olanisgmbh/regreen_sensolab/Infografiken/sensolab_proto_1.jpg

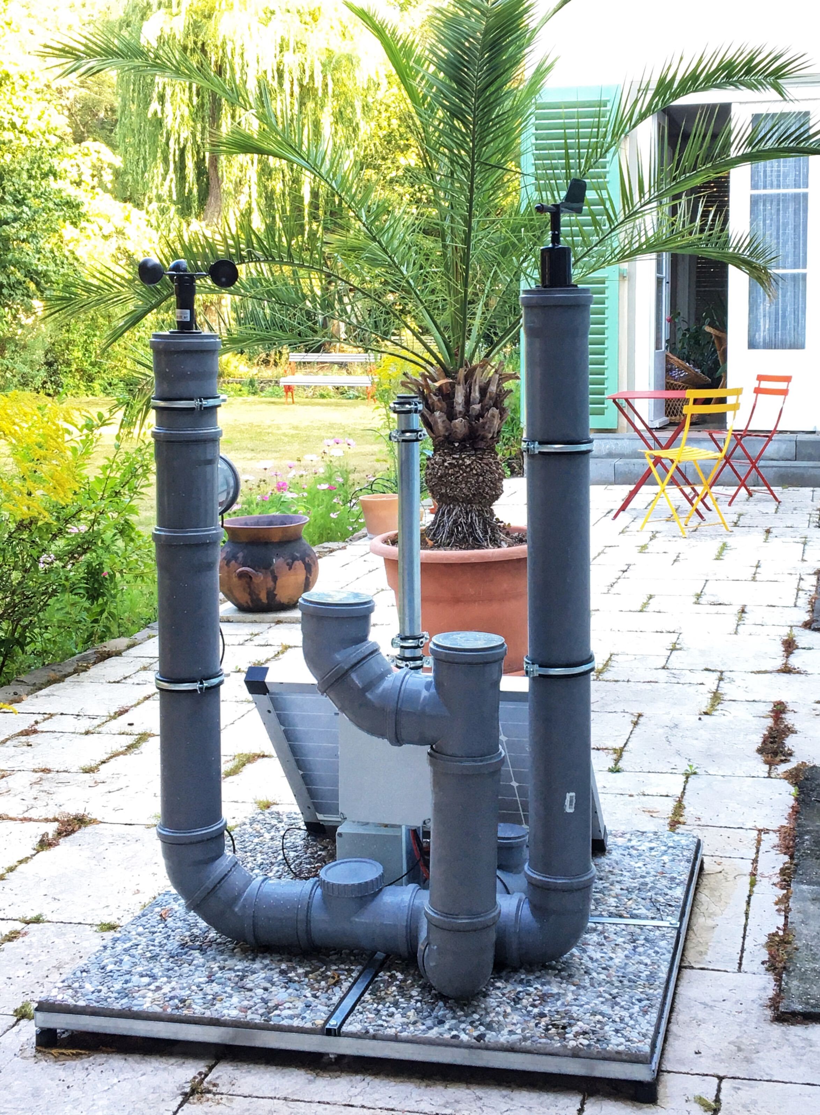
Infografiken/sensolab_proto_1.jpg
