olanisgmbh/regreen_sensolab/light-dome module/images/lightdome_01.jpg

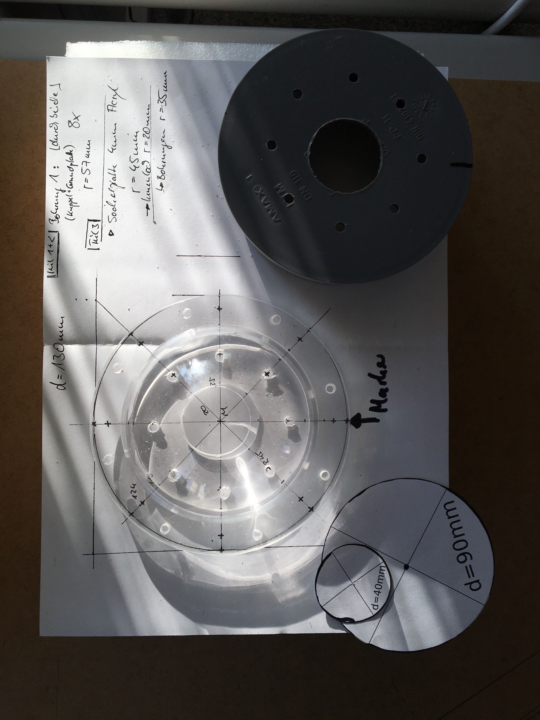
light-dome module/images/lightdome_01.jpg
