olanisgmbh/regreen_sensolab/light-dome module/KiCAD/Lightdome_SensorPCB/Lightdome_SensorPCB_wh.png

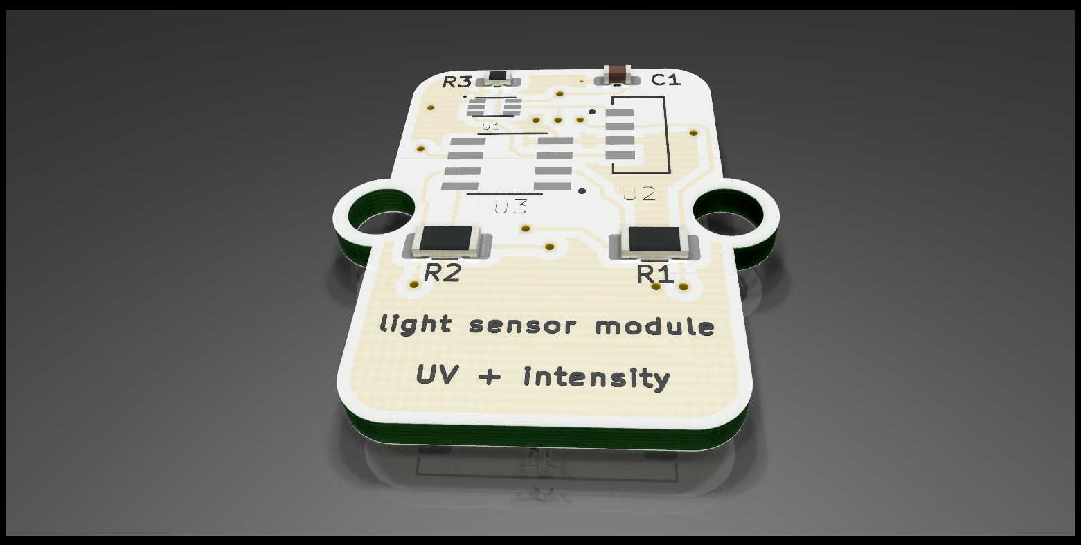
light-dome module/KiCAD/Lightdome_SensorPCB/Lightdome_SensorPCB_wh.png
