olanisgmbh/regreen_sensolab/LoRaWAN stuff/Screenshot at 2020-06-05 12-15-55.png

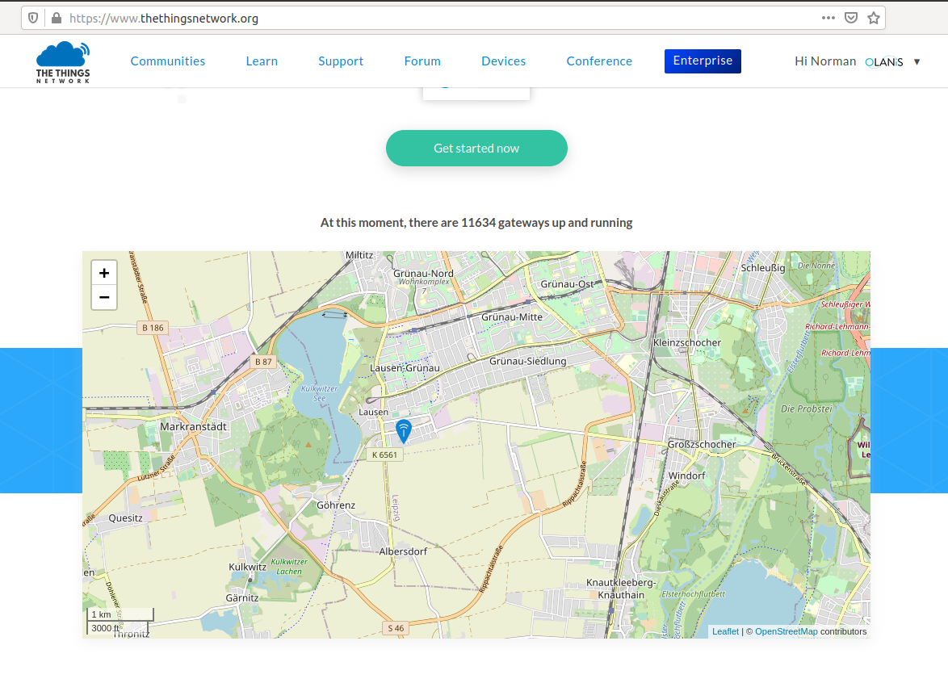
LoRaWAN stuff/Screenshot at 2020-06-05 12-15-55.png
