olanisgmbh/regreen_sensolab/LoRaWAN stuff/Screenshot at 2020-06-05 12-48-13.png

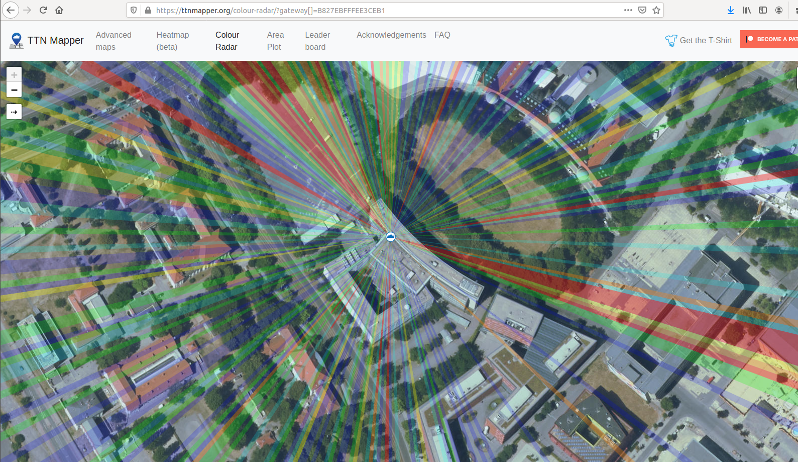
LoRaWAN stuff/Screenshot at 2020-06-05 12-48-13.png
