olanisgmbh/regreen_sensolab/LoRaWAN stuff/Screenshot at 2020-06-05 12-54-40.png

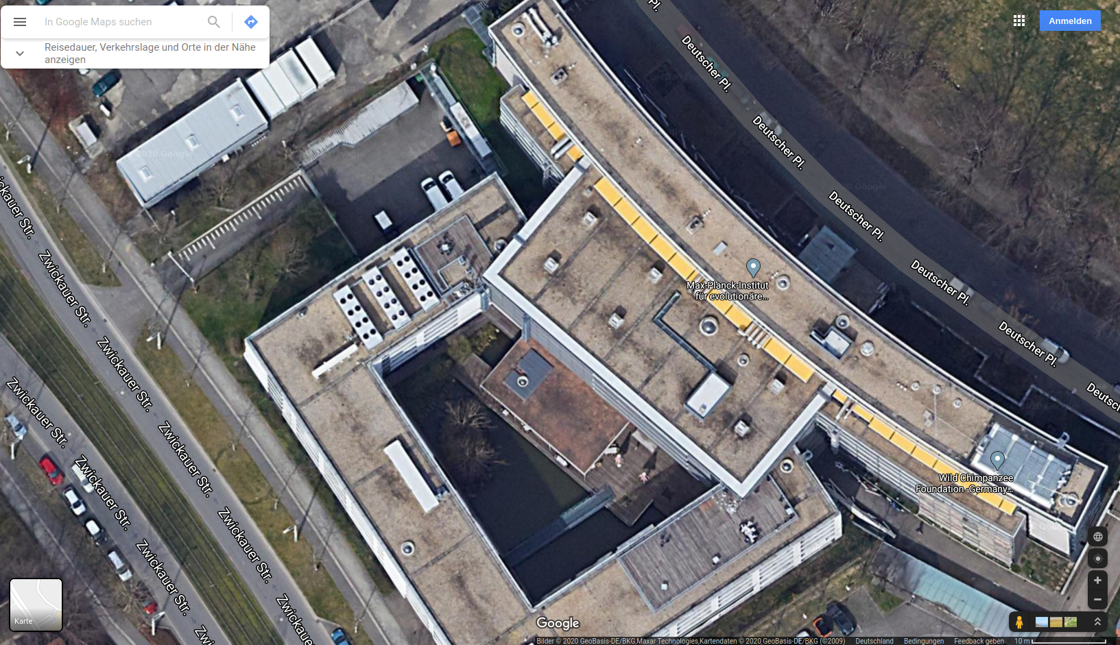
LoRaWAN stuff/Screenshot at 2020-06-05 12-54-40.png
