olanisgmbh/regreen_sensolab/LoRaWAN stuff/Screenshot at 2020-06-05 13-23-22.png

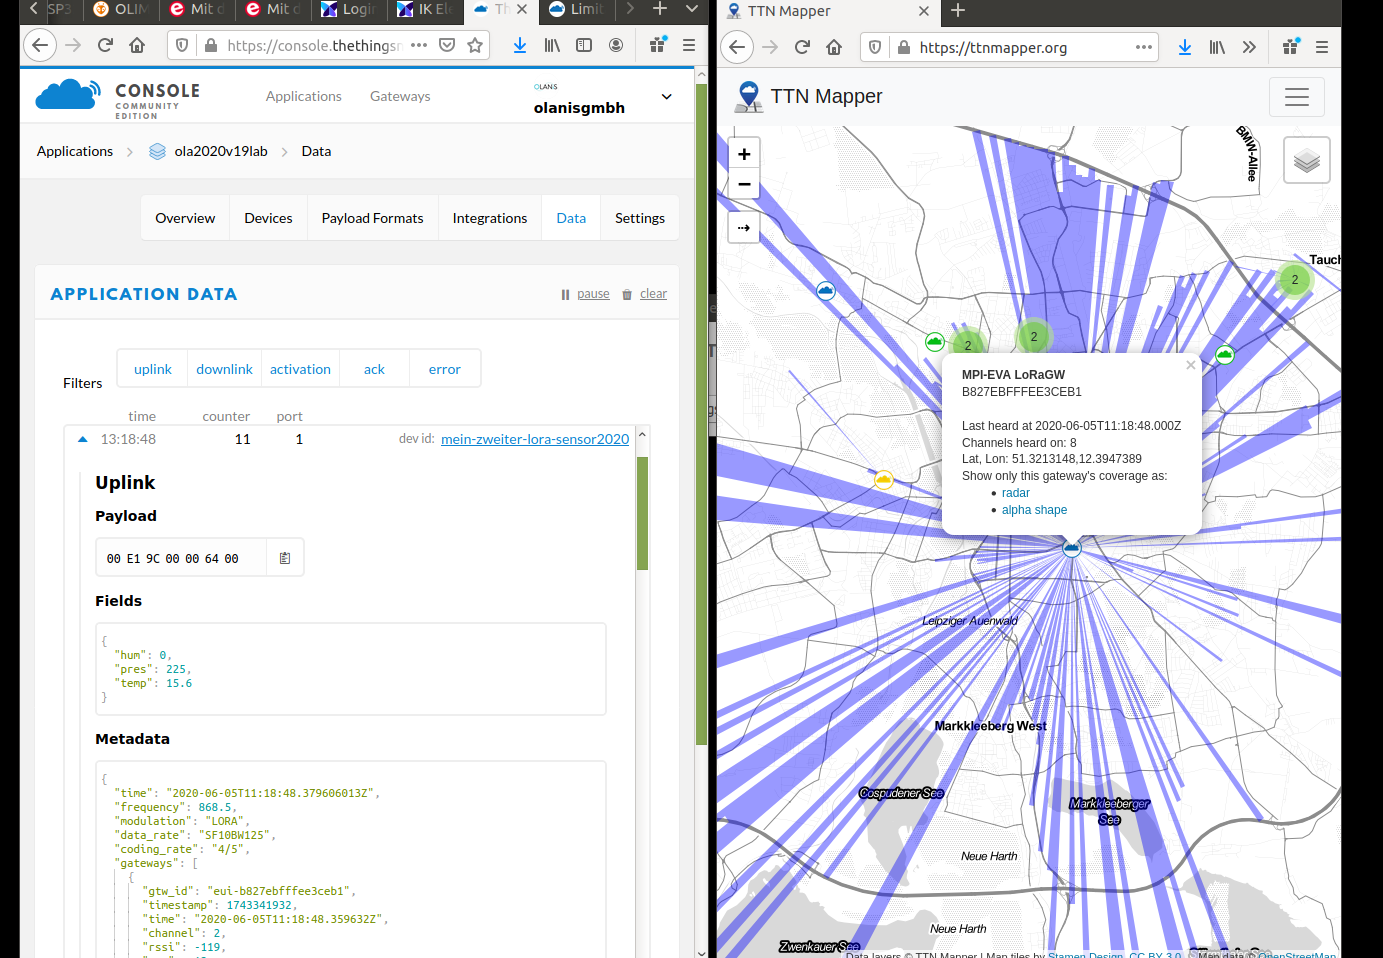
LoRaWAN stuff/Screenshot at 2020-06-05 13-23-22.png
