olanisgmbh/regreen_sensolab/LoRaWAN stuff/Screenshot at 2020-06-05 18-40-18.png

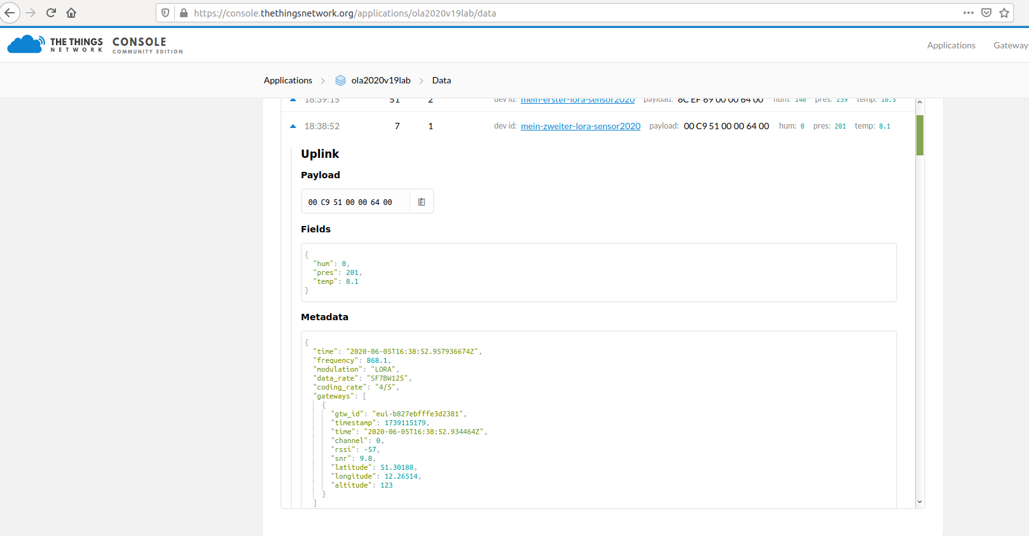
LoRaWAN stuff/Screenshot at 2020-06-05 18-40-18.png
