olanisgmbh/regreen_sensolab/LoRaWAN stuff/Screenshot at 2020-06-05 19-55-03.png

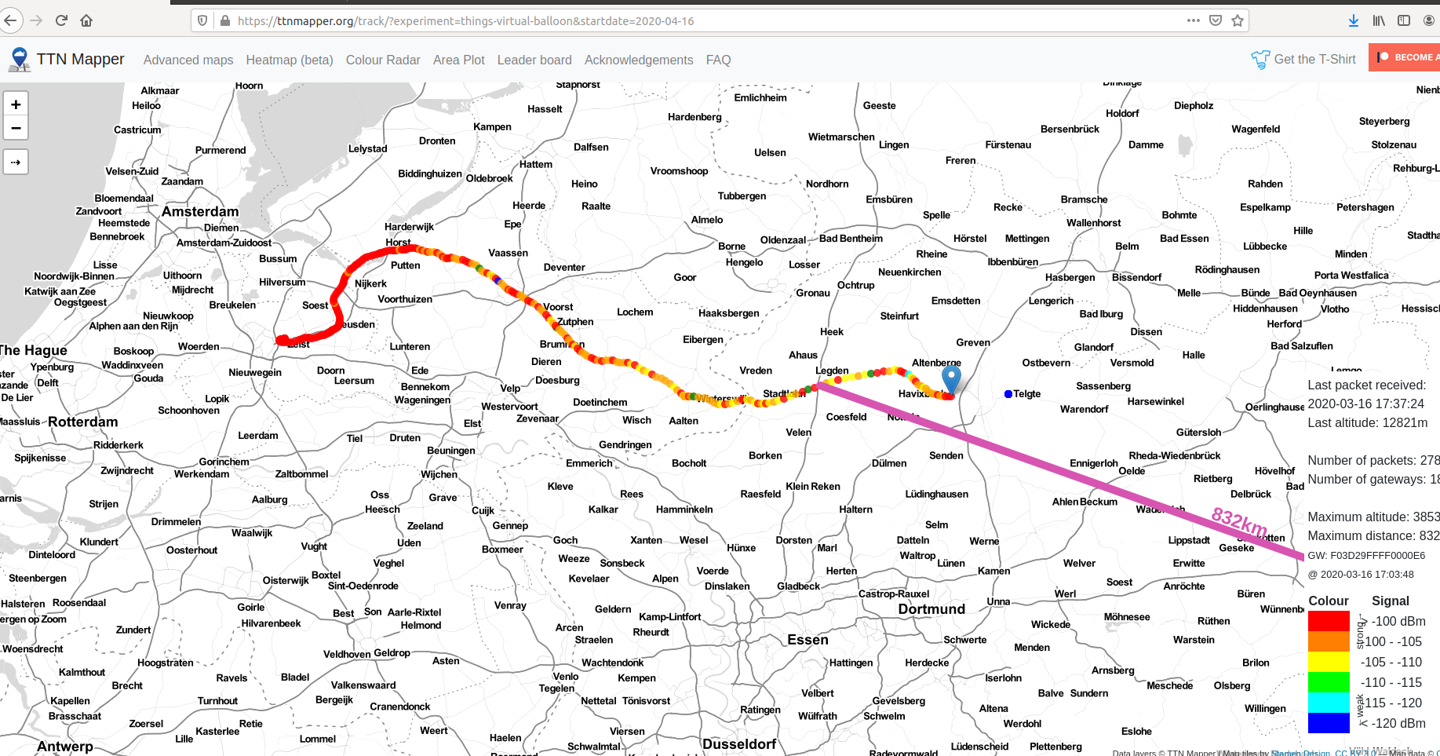
LoRaWAN stuff/Screenshot at 2020-06-05 19-55-03.png
