olanisgmbh/regreen_sensolab/LoRaWAN stuff/Screenshot at 2020-06-10 13-29-07.png

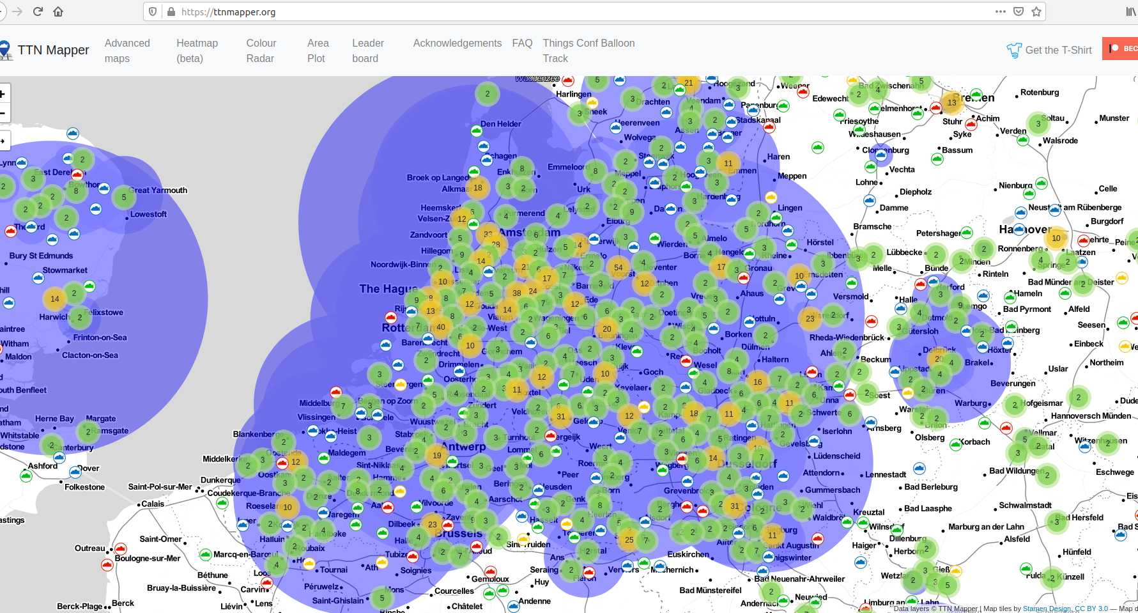
LoRaWAN stuff/Screenshot at 2020-06-10 13-29-07.png
