olanisgmbh/regreen_sensolab/solar panel mount/images/image01.jpg

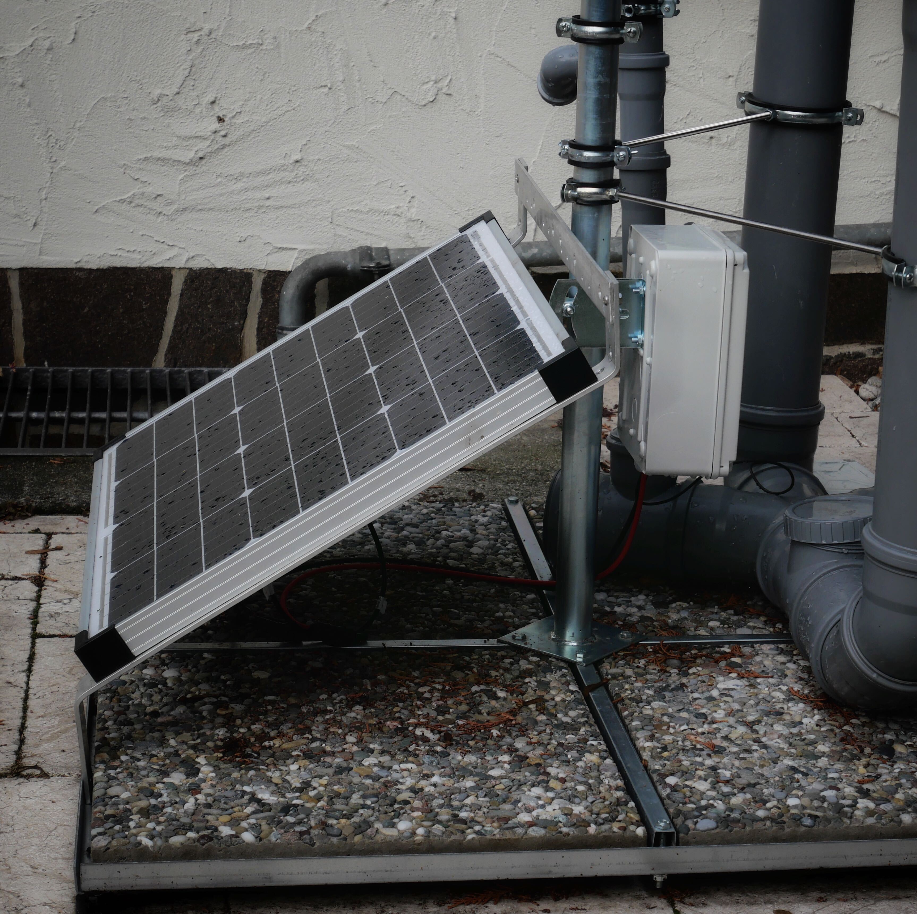
solar panel mount/images/image01.jpg
