olanisgmbh/regreen_sensolab/solar panel mount/images/image02.jpg

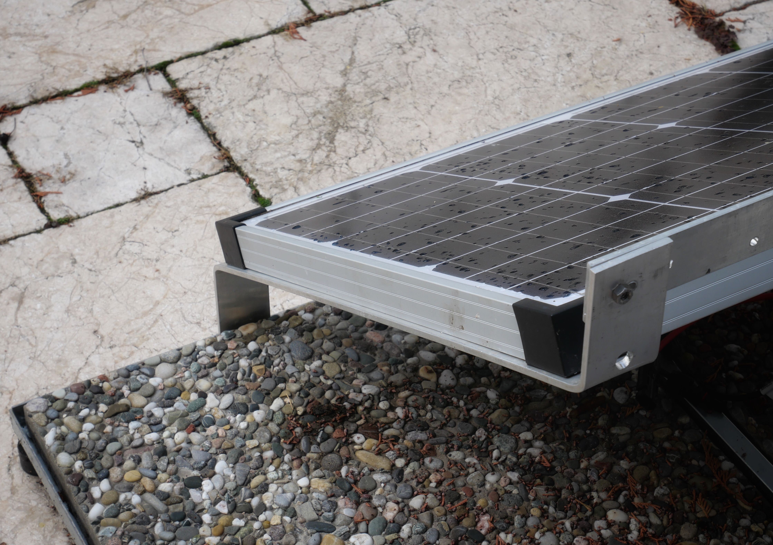
solar panel mount/images/image02.jpg
