olanisgmbh/regreen_sensolab/solar panel mount/images/image03.jpg

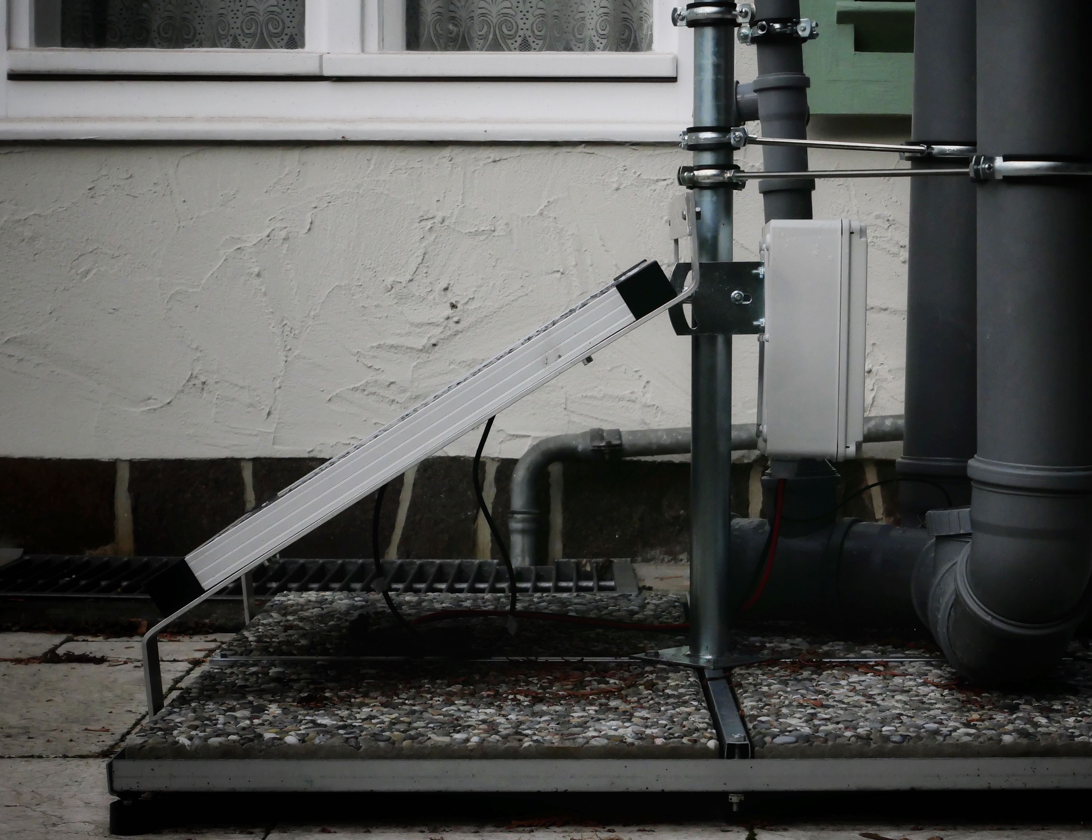
solar panel mount/images/image03.jpg
