olanisgmbh/regreen_sensolab/solar panel mount/images/image04.jpg

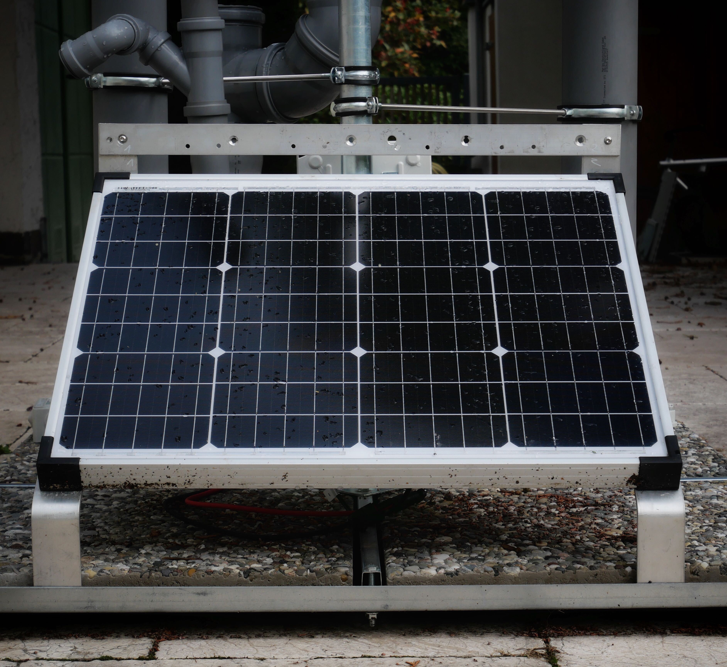
solar panel mount/images/image04.jpg
