olanisgmbh/regreen_sensolab/light-dome module/drawings/pdf/lightdome_assembly_explo.png

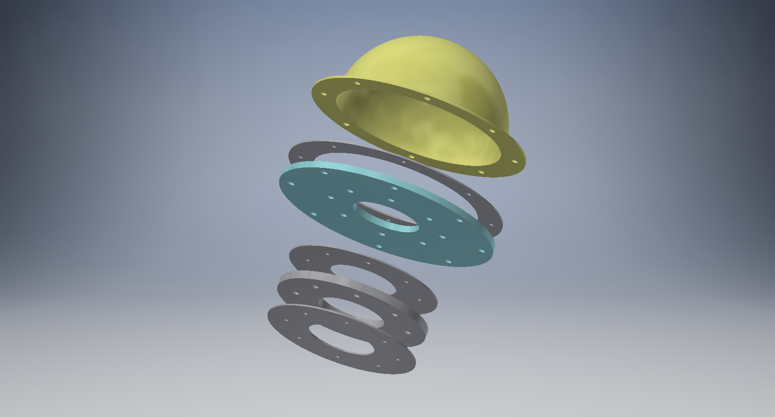
light-dome module/drawings/pdf/lightdome_assembly_explo.png
