olanisgmbh/regreen_sensolab/radiation shield and weather module/radiation shield/Radiation_Shield_assembly.png

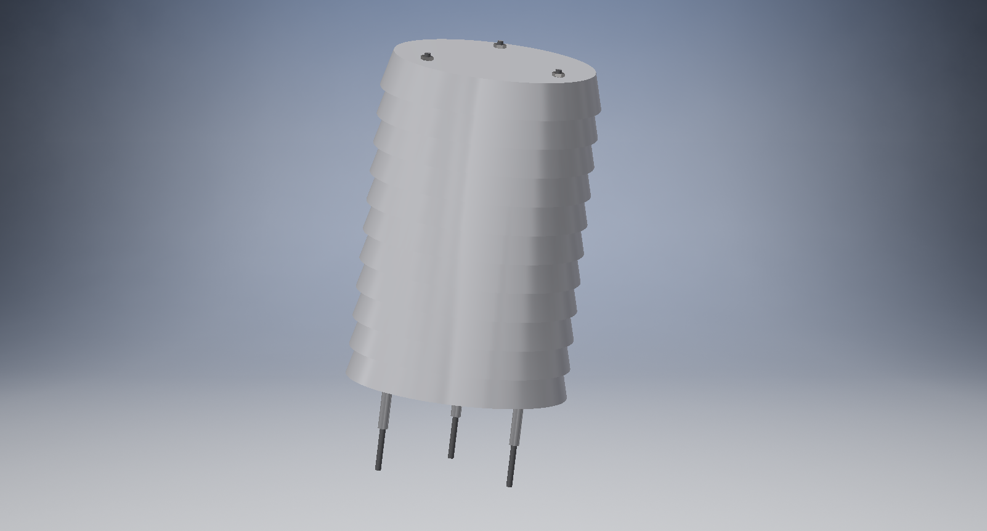
radiation shield and weather module/radiation shield/Radiation_Shield_assembly.png
