olanisgmbh/regreen_sensolab/radiation shield and weather module/radiation shield/Radiation_Shield_assembly_4.png

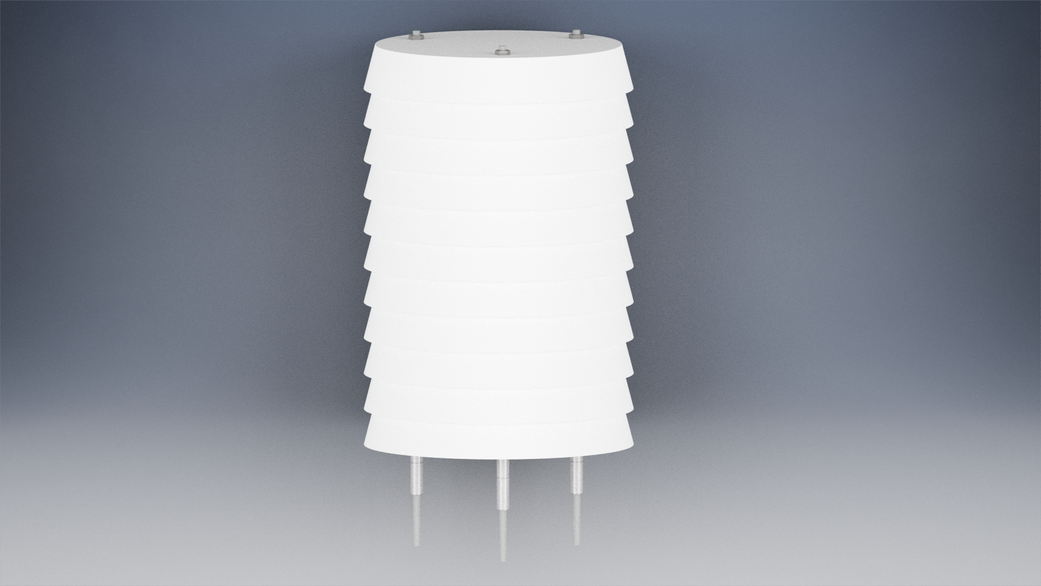
radiation shield and weather module/radiation shield/Radiation_Shield_assembly_4.png
