olanisgmbh/regreen_sensolab/Regreen_Sensolab_TubeCase/Tubes_assembly_LDandRS.png

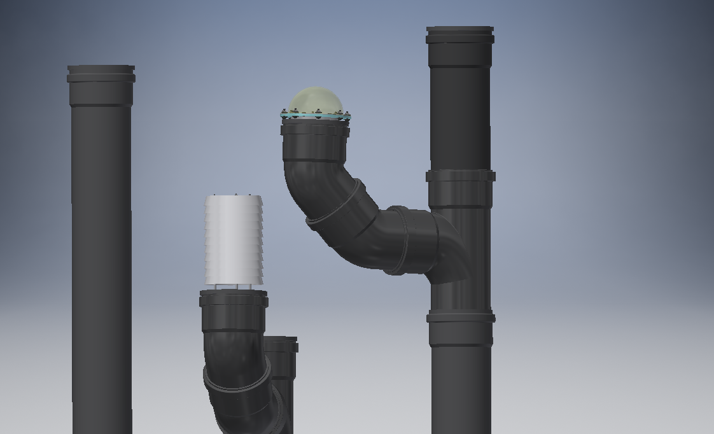
Regreen_Sensolab_TubeCase/Tubes_assembly_LDandRS.png
