olanisgmbh/regreen_sensolab/radiation shield and weather module/radiation shield/radiation_shield_dish.pdf

⌀100.00 mm

⌀3.00 mm

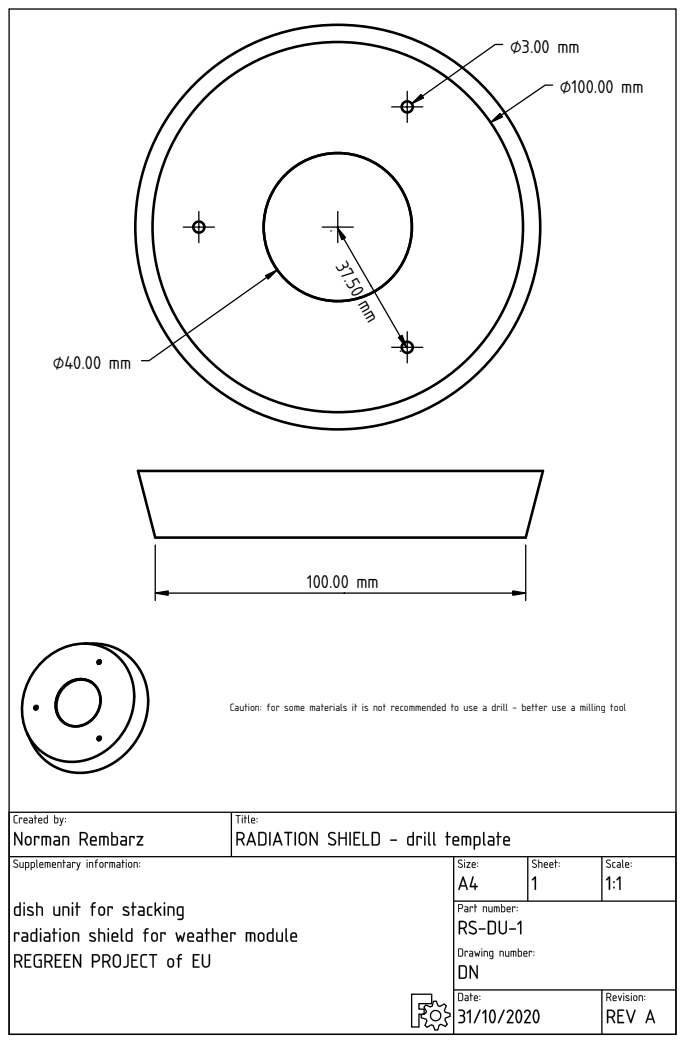
[picture p59: page 1]

Caution: for some materials it is not recommended to use a drill - better use a milling tool
