olanisgmbh/regreen_sensolab/radiation shield and weather module/radiation shield/radiation_shield_dish_top.pdf

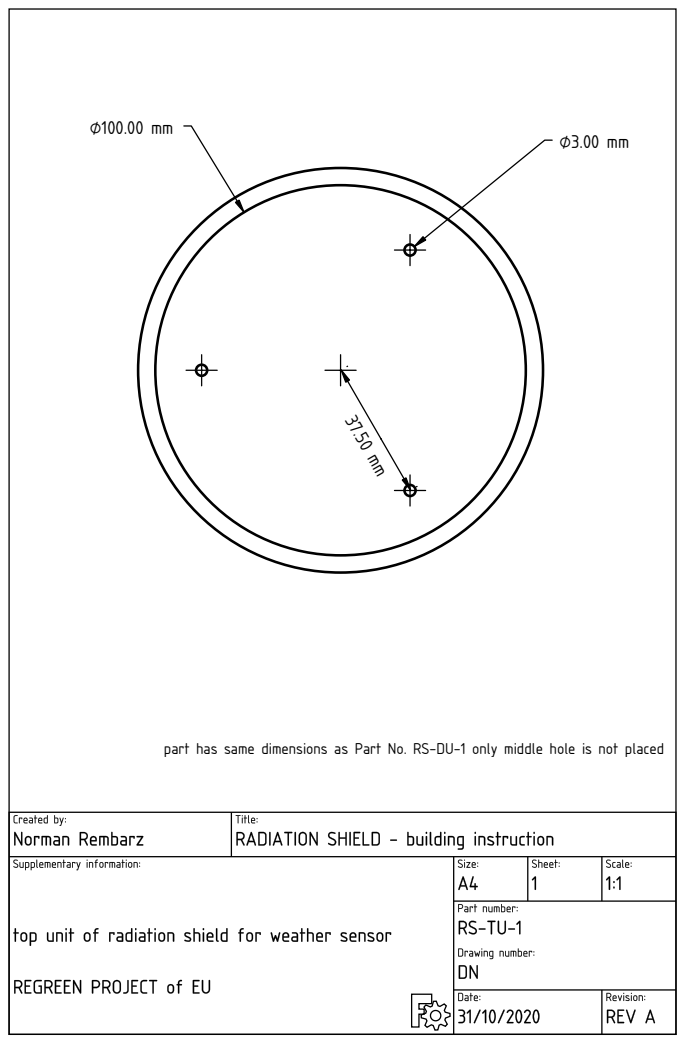
[picture p60: page 1]

part has same dimensions as Part No. RS-DU-1 only middle hole is not placed
