olanisgmbh/regreen_sensolab/light-dome module/drawings/pdf/Acryl_Ring_spacer_LightDome.PDF

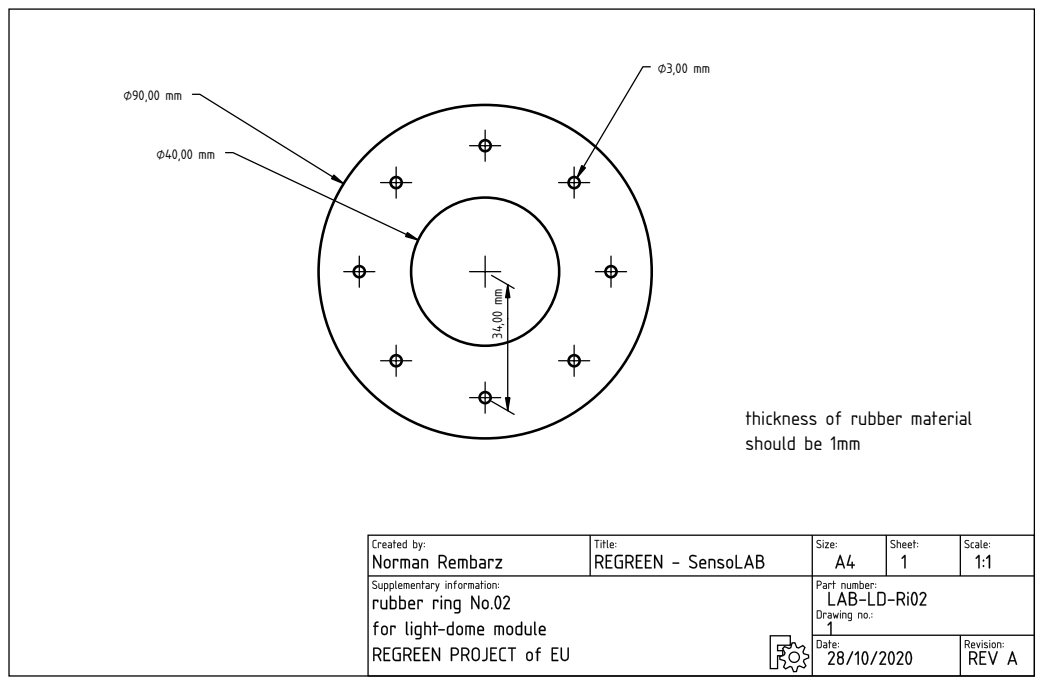
[picture p61: page 1]

thickness of rubber material
should be 1mm
