olanisgmbh/regreen_sensolab/light-dome module/drawings/pdf/Kuppel_Lightdome_part.pdf

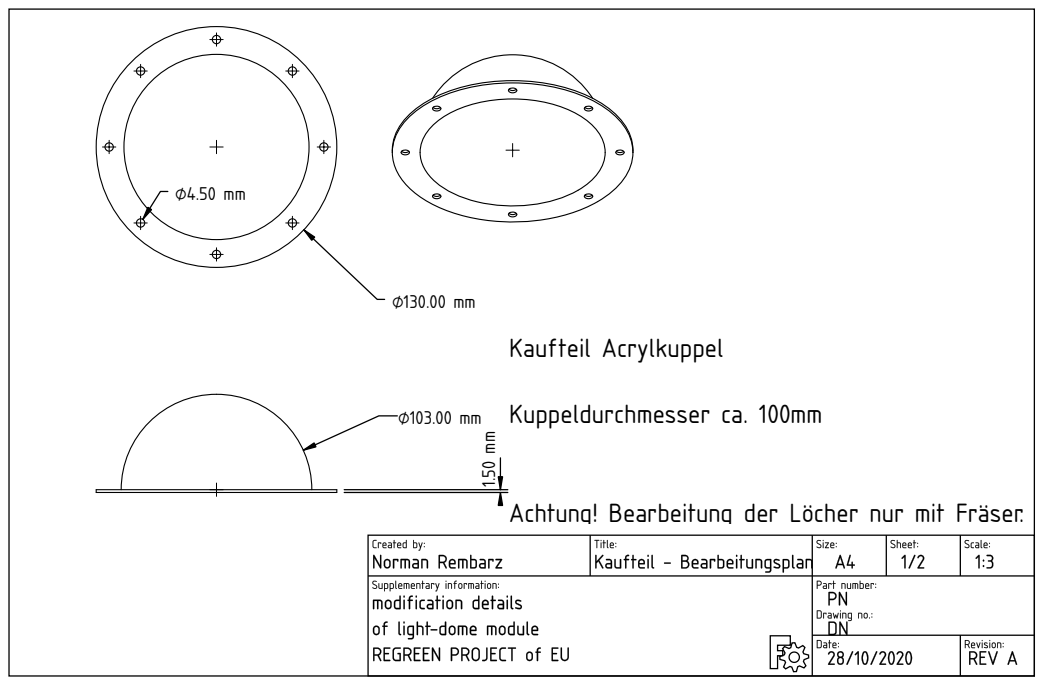
[picture p62: page 1]
Kaufteil Acrylkuppel; Kuppeldurchmesser ca. 100mm

Achtung! Bearbeitung der Löcher nur mit Fräser.
