olanisgmbh/regreen_sensolab/light-dome module/drawings/pdf/Rubber_Ring_I_LightDome.PDF

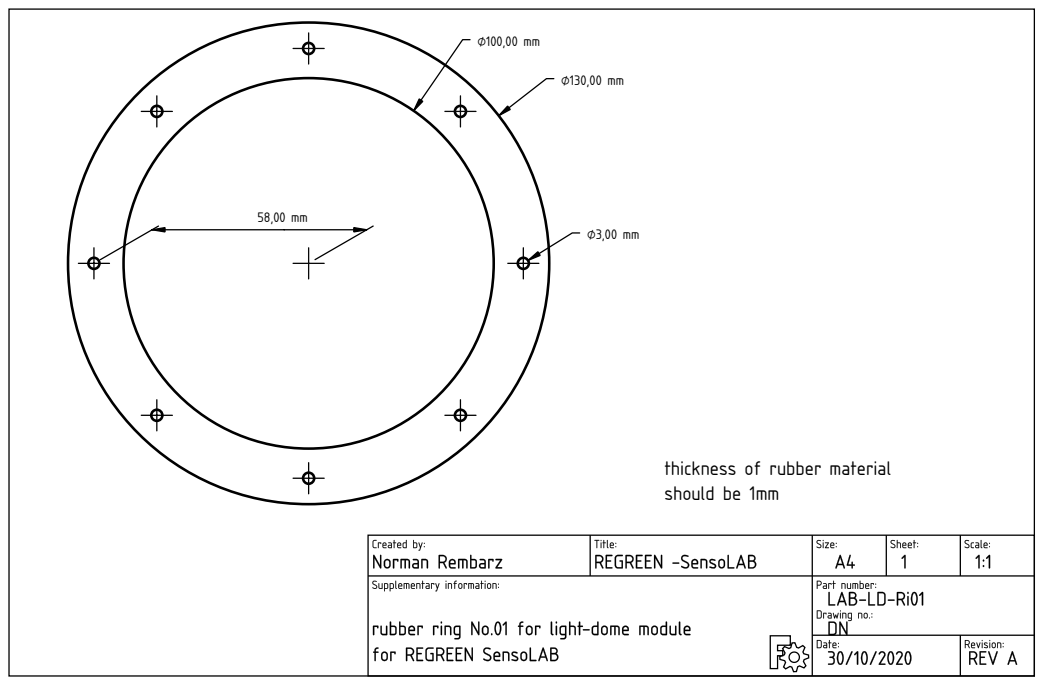
[picture p63: page 1]

thickness of rubber material
should be 1mm
