olanisgmbh/regreen_sensolab/light-dome module/drawings/pdf/Rubber_Ring_II_LightDome.pdf

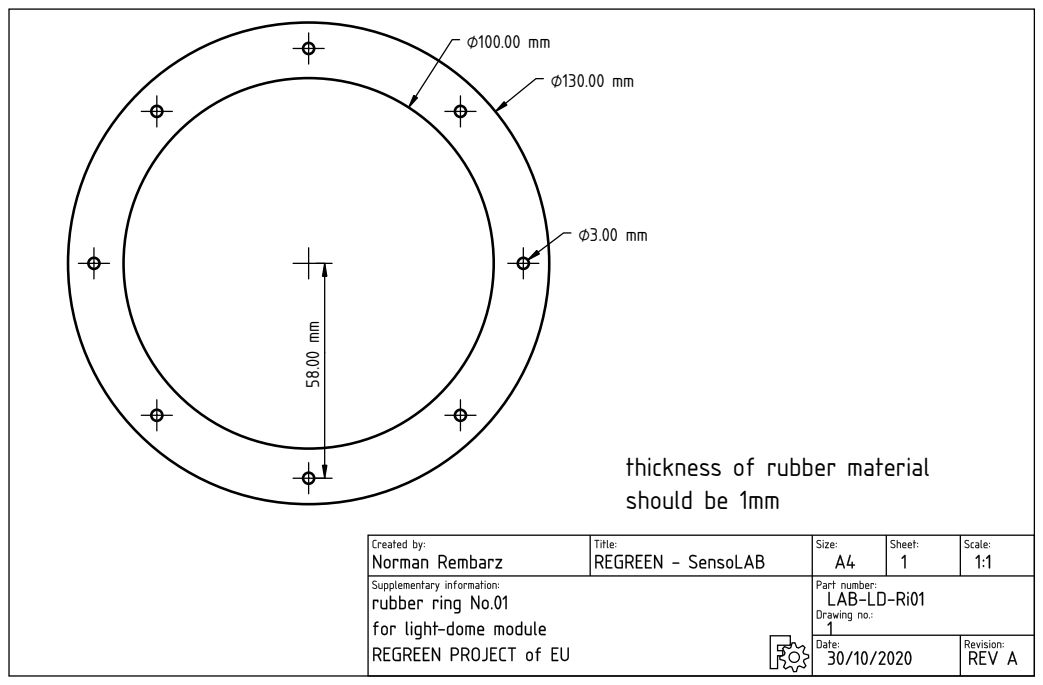
[picture p64: page 1]

thickness of rubber material
should be 1mm
