olanisgmbh/regreen_sensolab/light-dome module/drawings/pdf/top_plate_LightDome.PDF

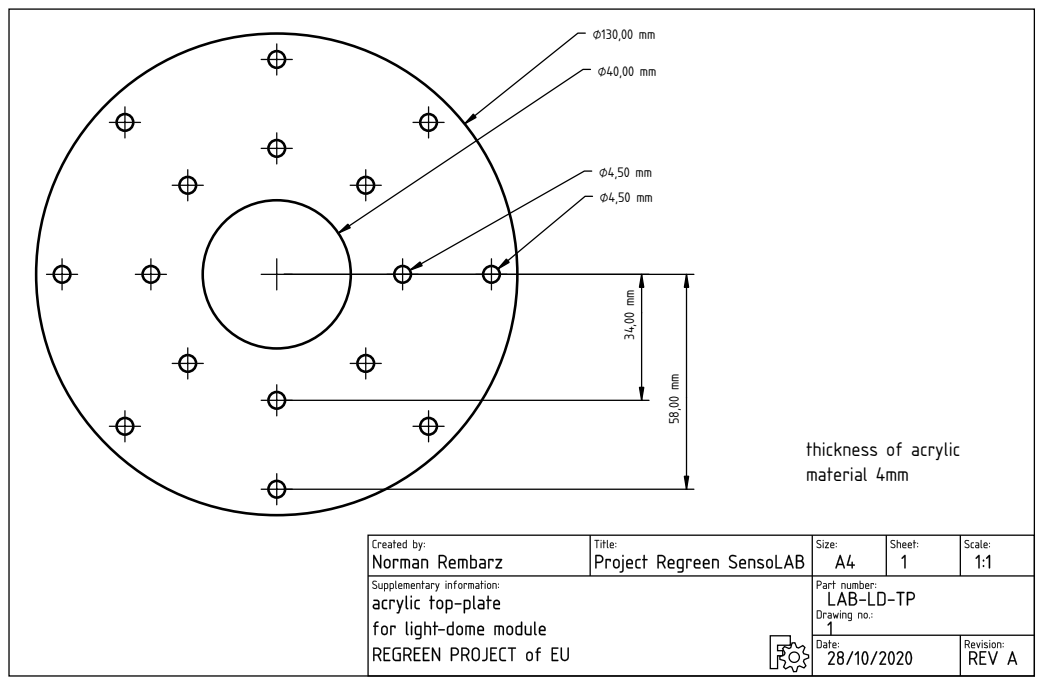
[picture p65: page 1]

thickness of acrylic
material 4mm
