olanisgmbh/regreen_sensolab/solar panel mount/drawings/solar_panel_mount_bracket_1_Biegung.PDF

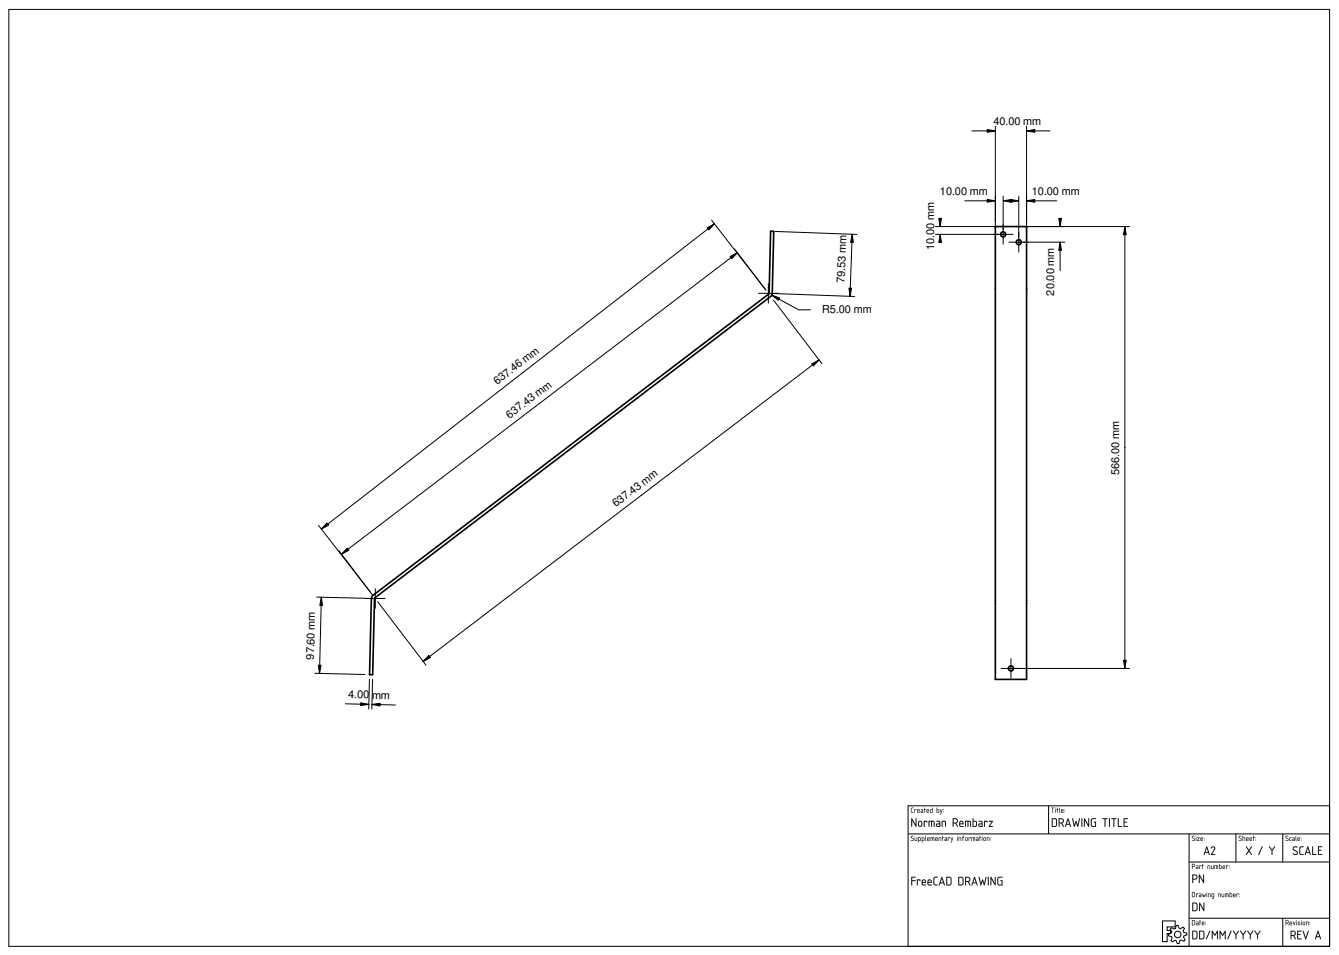
[picture p70: page 1]
