olanisgmbh/regreen_sensolab/solar panel mount/drawings/solar_panel_mount_bracket_2.PDF

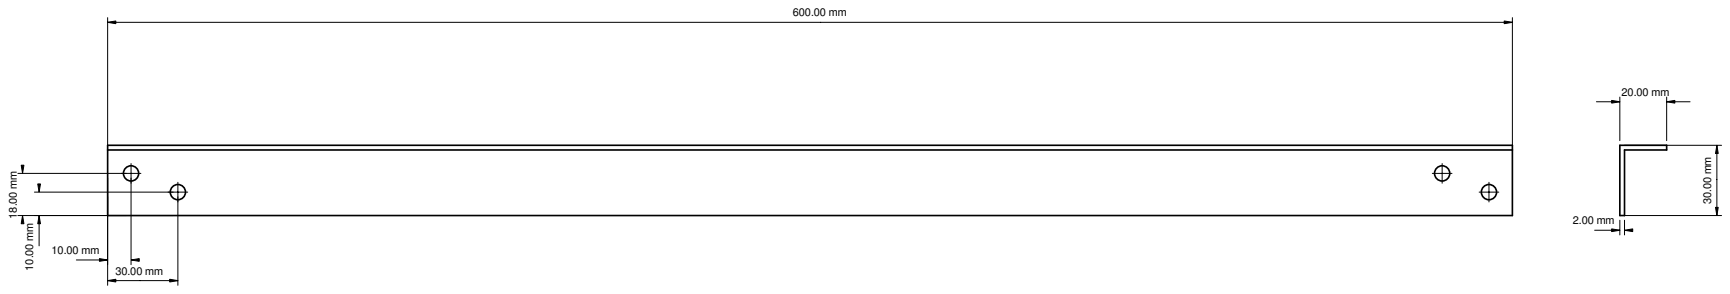
[picture p71: page 1]
