olanisgmbh/regreen_sensolab/light-dome module/drawings/pdf/Kuppel_Lightdome_Schablone.pdf

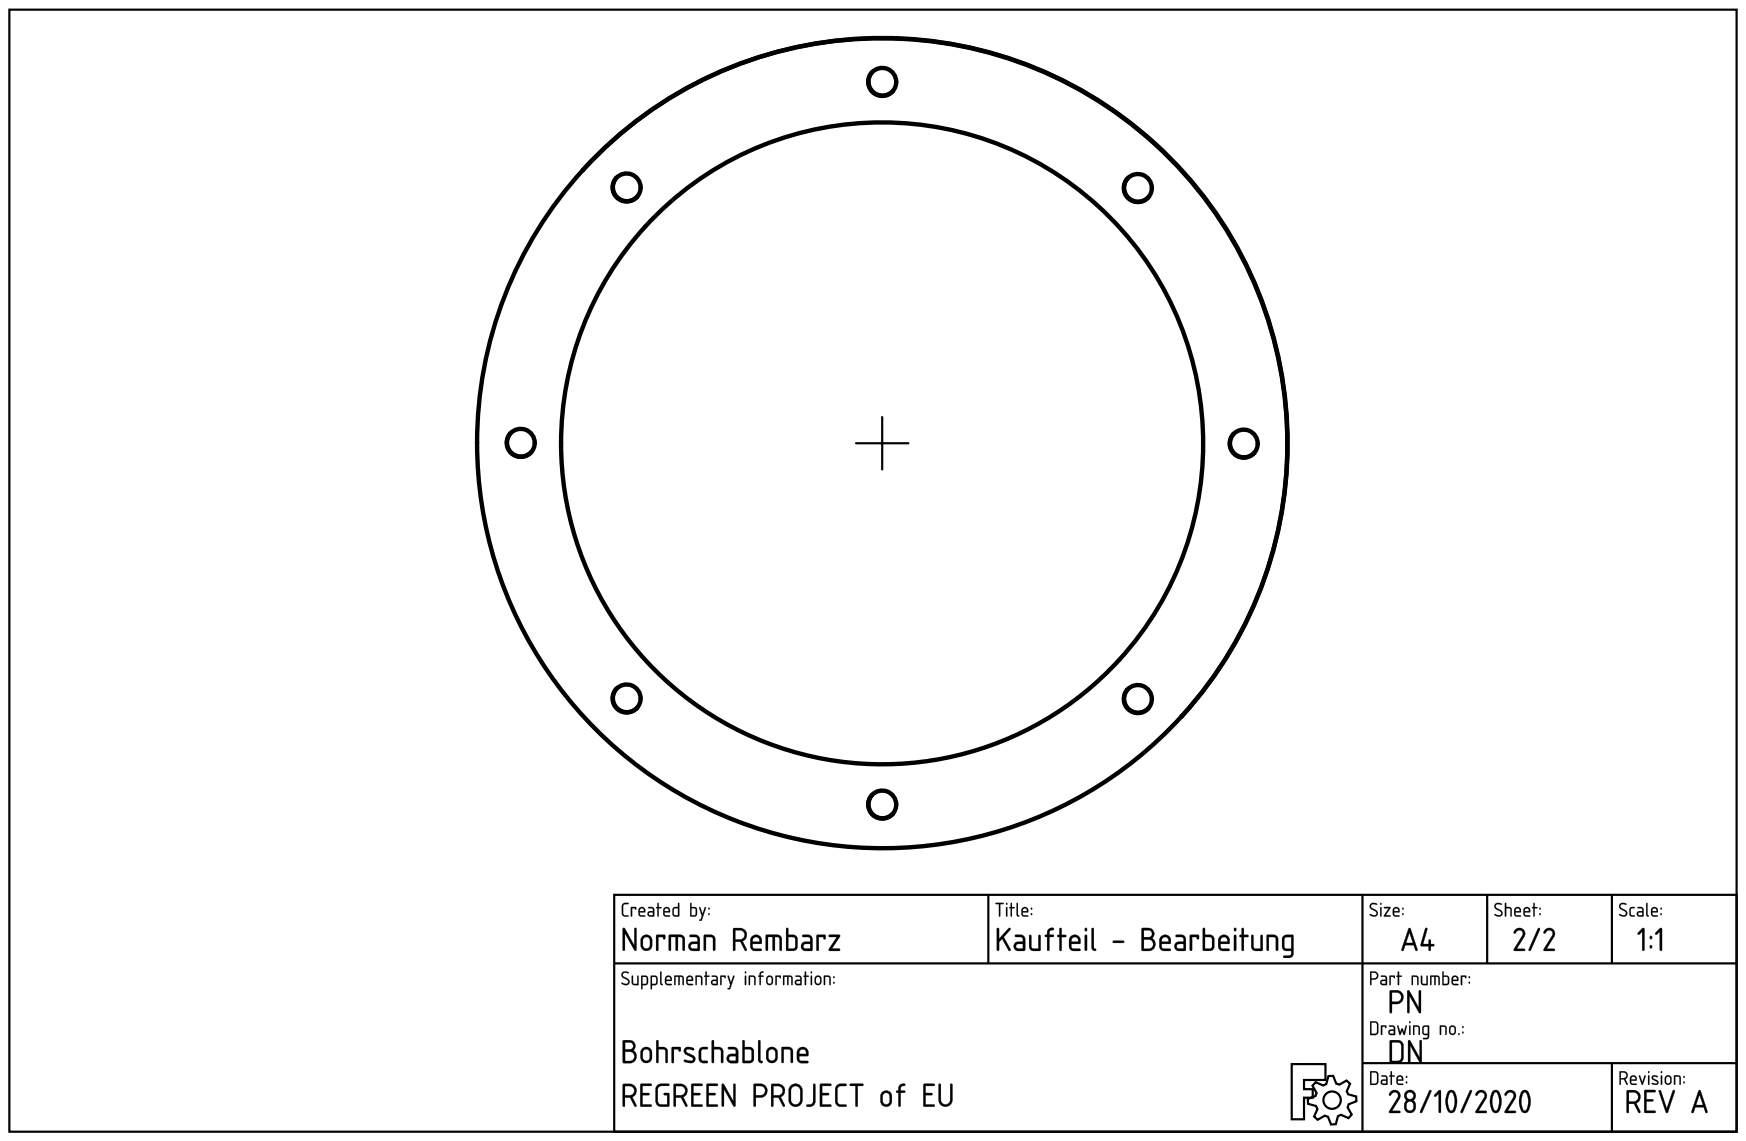
[picture p72: page 1]
